lipoyang/M5Gurdy/src/Icon_Volume.h

const unsigned short ICON_VOLUME[] = {
    // w,h: 36 36
    0x0000,0x0000,0x0000,0x0000,0x0000,0x0000,0x0000,0x0000,
    0x0000,0x0000,0x0000,0x0000,0x0000,0x0000,0x0000,0x0000,
    0x0000,0x0000,0x0000,0x18E3,0x39C7,0x0000,0x0000,0x0000,
    0x0000,0x0000,0xA534,0xBDF7,0x2104,0x0000,0x0000,0x0000,
    0x0000,0x0000,0x0000,0x0000,
    0x0000,0x0000,0x0000,0x0000,0x0000,0x0000,0x0000,0x0000,
    0x0000,0x0000,0x0000,0x0000,0x0000,0x0000,0x0000,0x0000,
    0x0000,0x0000,0x52AA,0xF7BE,0xFFFF,0xBDD7,0x0000,0x0000,
    0x0000,0x0861,0xFFFF,0xFFFF,0xEF7D,0x39E7,0x0000,0x0000,
    0x0000,0x0000,0x0000,0x0000,
    0x0000,0x0000,0x0000,0x0000,0x0000,0x0000,0x0000,0x0000,
    0x0000,0x0000,0x0000,0x0000,0x0000,0x0000,0x0000,0x0000,
    0x0000,0x632C,0xFFFF,0xFFFF,0xFFFF,0xFFFF,0x5269,0x0000,
    0x0000,0x0000,0xB596,0xFFFF,0xFFFF,0xF7BE,0x4208,0x0000,
    0x0000,0x0000,0x0000,0x0000,
    0x0000,0x0000,0x0000,0x0000,0x0000,0x0000,0x0000,0x0000,
    0x0000,0x0000,0x0000,0x0000,0x0000,0x0000,0x0000,0x0000,
    0x7BCF,0xFFFF,0xFFFF,0xFFFF,0xFFFF,0xFFFF,0x7BEF,0x0000,
    0x0000,0x0000,0x0000,0x8410,0xFFFF,0xFFFF,0xF79E,0x2945,
    0x0000,0x0000,0x0000,0x0000,
    0x0000,0x0000,0x0000,0x0000,0x0000,0x0000,0x0000,0x0000,
    0x0000,0x0000,0x0000,0x0000,0x0000,0x0000,0x0000,0x8C71,
    0xFFFF,0xFFFF,0xFFFF,0xFFFF,0xFFFF,0xFFFF,0x8410,0x0000,
    0x0000,0x0000,0x0000,0x0000,0x632C,0xFFFF,0xFFFF,0xD6BA,
    0x0841,0x0000,0x0000,0x0000,
    0x0000,0x0000,0x0000,0x0000,0x0000,0x0000,0x0000,0x0000,
    0x0000,0x0000,0x0000,0x0000,0x0000,0x0020,0xA513,0xFFFF,
    0xFFFF,0xFFFF,0xFFFF,0xFFFF,0xFFFF,0xFFFF,0x8410,0x0000,
    0x0000,0x0000,0x0000,0x0000,0x0000,0x7BCF,0xFFFF,0xFFFF,
    0x8C71,0x0000,0x0000,0x0000,
    0x0000,0x0000,0x0000,0x0000,0x0000,0x0000,0x0000,0x0000,
    0x0000,0x0000,0x0000,0x0000,0x0841,0xAD75,0xFFFF,0xFFFF,
    0xFFFF,0xFFFF,0xFFFF,0xFFFF,0xFFFF,0xFFFF,0x8410,0x0000,
    0x0000,0x0000,0x0000,0x0000,0x0000,0x0000,0xB5B6,0xFFFF,
    0xFFDF,0x2945,0x0000,0x0000,
    0x0000,0x0000,0x0000,0x0000,0x0000,0x0000,0x0000,0x0000,
    0x0000,0x0000,0x0000,0x0861,0xBDF7,0xFFFF,0xFFFF,0xFFFF,
    0xFFFF,0xFFFF,0xFFFF,0xFFFF,0xFFFF,0xFFFF,0x8410,0x0000,
    0x0000,0x0000,0x0000,0x0000,0x0000,0x0000,0x18E3,0xF79E,
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
};
