lipoyang/M5Gurdy/src/DisplayUI.cpp

#include <M5Stack.h>
#include <PollingTimer.h>
#include "DisplayUI.h"
#include "Icon_Scale.h"
#include "Icon_Volume.h"

// 外部参照
extern int master_vol;      // マスター音量
extern int tone_no;         // 音色
extern int scale;           // 音階(ハ長調からどれだけ上がるか下がるか)

// 描画位置
#define X_TONE      10
#define Y_TONE      10
#define W_TONE      300
#define P_TONE      24
#define X_SCALE     10
#define Y_SCALE     170
#define W_SCALE     140
#define P_SCALE     60
#define X_VOLUME    170
#define Y_VOLUME    170
#define W_VOLUME    140
#define P_VOLUME    60
#define X_KEY       120
#define Y_KEY       80
#define W_KEY       100
#define H_KEY       64
#define H_CHAR      48
#define R_CHAR      5
#define X_ERROR     10
#define Y_ERROR1    65
#define Y_ERROR2    115
#define W_ERROR     300
#define H_ERROR     100
#define P_ICON      12

// スプライト
TFT_eSprite spriteKey    = TFT_eSprite(&M5.Lcd);
TFT_eSprite spriteTone   = TFT_eSprite(&M5.Lcd);
TFT_eSprite spriteScale  = TFT_eSprite(&M5.Lcd);
TFT_eSprite spriteVolume = TFT_eSprite(&M5.Lcd);
TFT_eSprite spriteError  = TFT_eSprite(&M5.Lcd);

// ポップアップ表示
bool isPopup = false;
OneShotTimer popupTimer;

// サブルーチン
static void DisplayUI_frame();
static void DisplayUI_sound(int octave, int key12, int vol);

// 初期化
void DisplayUI_begin()
{
    M5.begin(true, false, true); // LCD:ON, SDカード:OFF, シリアル:ON
//  M5.Power.begin();
//  M5.Speaker.setVolume(0);
//  M5.Lcd.setBrightness(200);
    M5.Lcd.setRotation(3); // 180度回転

    M5.Lcd.fillScreen(BLACK);

    // スプライトの作成
    spriteKey.setColorDepth(16);
    spriteKey.createSprite(W_KEY, H_KEY);
    spriteKey.setTextFont(2);
    spriteKey.setTextSize(4);

    spriteTone.setColorDepth(16);
    spriteTone.createSprite(W_TONE - P_TONE, H_CHAR);
    spriteTone.setTextFont(2);
    spriteTone.setTextSize(3);

    spriteScale.setColorDepth(16);
    spriteScale.createSprite(W_SCALE - P_SCALE, H_CHAR);
    spriteScale.setTextFont(2);
    spriteScale.setTextSize(3);

    spriteVolume.setColorDepth(16);
    spriteVolume.createSprite(W_VOLUME - P_VOLUME, H_CHAR);
    spriteVolume.setTextFont(2);
    spriteVolume.setTextSize(3);

    spriteError.setColorDepth(16);
    spriteError.createSprite(W_ERROR, H_ERROR);
    spriteError.setTextFont(2);
    spriteError.setTextSize(3);

    DisplayUI_frame();
    DisplayUI_settings();
}

// メインループ処理
void DisplayUI_loop(int octave, int key12, int vol)
{
    M5.update();
    
    // ボタン入力判定とそれに対する処理
    if (M5.BtnA.wasPressed()) {
    }
    if (M5.BtnB.wasPressed()){
    }
    if(M5.BtnC.wasPressed()){
    }
    
    // サウンド出力の描画
    static int cnt = 0;
    cnt++;
    if(cnt >= 4){
        cnt = 0;
        if(!isPopup){
            DisplayUI_sound(octave, key12, vol);
        }
    }
    // ポップアップの解除
    if(isPopup && popupTimer.elapsed()){
        isPopup = false;
        DisplayUI_error("");
    }
}

// 枠線の描画
static void DisplayUI_frame()
{
    M5.Lcd.drawRoundRect(
        X_TONE - R_CHAR, Y_TONE - R_CHAR,
        W_TONE + R_CHAR * 2, H_CHAR + R_CHAR * 2,
        R_CHAR, WHITE);//YELLOW); 
    M5.Lcd.drawRoundRect(
        X_SCALE - R_CHAR, Y_SCALE - R_CHAR,
        W_SCALE + R_CHAR * 2, H_CHAR + R_CHAR * 2,
        R_CHAR, WHITE);//YELLOW); 
    M5.Lcd.drawRoundRect(
        X_VOLUME - R_CHAR, Y_VOLUME - R_CHAR,
        W_VOLUME + R_CHAR * 2, H_CHAR + R_CHAR * 2,
        R_CHAR, WHITE);//YELLOW); 

    M5.Lcd.drawBitmap(X_TONE + P_ICON, Y_SCALE + 6, 36, 36, ICON_SCALE);
    M5.Lcd.drawBitmap(X_VOLUME + P_ICON, Y_SCALE + 6, 36, 36, ICON_VOLUME);
}

// 設定の描画
void DisplayUI_settings()
{
    // 音色名
    static const char TONE_NAME[][13] = {
        "Strings",
        "Bagpipes",
        "Church Organ",
        "Accordion",
        "Flute",
        "Trumpet",
        "Synthesizer",
        "String Synth",
        "Chorus",
    };

    // 音色
    spriteTone.setTextColor(YELLOW); //, BLACK);
    spriteTone.fillRect(0,0,W_TONE - P_TONE,H_CHAR,BLACK);
    spriteTone.setCursor(0,0);
    spriteTone.print(TONE_NAME[tone_no]);
    spriteTone.pushSprite(X_TONE + P_TONE, Y_TONE);

    // 調性
    spriteScale.setTextColor(YELLOW); //, BLACK);
    spriteScale.fillRect(0,0,W_SCALE - P_SCALE,H_CHAR,BLACK);
    spriteScale.setCursor(0,0);
    if(scale > 0){
        spriteScale.printf("+%d", scale);
    }else{
        spriteScale.printf("%d", scale);
    }
    spriteScale.pushSprite(X_SCALE + P_SCALE, Y_SCALE);

    // 音量
    spriteVolume.setTextColor(YELLOW); //, BLACK);
    spriteVolume.fillRect(0,0,W_VOLUME - P_VOLUME,H_CHAR,BLACK);
    spriteVolume.setCursor(0,0);
    // int vol = (master_vol >= 32) ? master_vol - 31 : 0;
    spriteVolume.printf("%d", master_vol);
    spriteVolume.pushSprite(X_VOLUME + P_VOLUME, Y_VOLUME);
}

// サウンドの描画
static void DisplayUI_sound(int octave, int key12, int vol)
{
    // オクターブごとの表示色のRGB値 (M5の色定数は5:6:5の16ビットカラー)
    static const uint16_t COLOR_TABLE[][3] = {
        { (RED    >> 11) & 0x1F, (RED    >> 5) & 0x3F, RED    & 0x1F }, // O2 赤色
        { (ORANGE >> 11) & 0x1F, (ORANGE >> 5) & 0x3F, ORANGE & 0x1F }, // O3 オレンジ色
        { (YELLOW >> 11) & 0x1F, (YELLOW >> 5) & 0x3F, YELLOW & 0x1F }, // O4 黄色
        { (GREEN  >> 11) & 0x1F, (GREEN  >> 5) & 0x3F, GREEN  & 0x1F }, // O5 緑色
        { (CYAN   >> 11) & 0x1F, (CYAN   >> 5) & 0x3F, CYAN   & 0x1F }, // O6 水色
    };
    // 音階の名前
    static const char KEY_NAME[12][3] = {
      "C", "C#", "D", "D#", "E", "F", "F#", "G", "G#", "A", "A#", "B" 
    };
    
    // 音量によって明度を変える
    int index = octave - 2;
    uint16_t r = COLOR_TABLE[index][0];
    uint16_t g = COLOR_TABLE[index][1];
    uint16_t b = COLOR_TABLE[index][2];
    const int VOL_SAT = 64; // 127以下の値で調整
    if(vol > VOL_SAT) vol = VOL_SAT;
    r = r * vol / VOL_SAT;
    g = g * vol / VOL_SAT;
    b = b * vol / VOL_SAT;
    uint16_t color = (r << 11) | (g << 5) | b;
    
#if 0
    M5.Lcd.fillRect(X_KEY,Y_KEY,W_KEY,H_KEY,BLACK);
    M5.Lcd.setTextColor(color);//, BLACK);
    M5.Lcd.setCursor(X_KEY,Y_KEY);
    M5.Lcd.setTextFont(2);
    M5.Lcd.setTextSize(4);
    M5.Lcd.print(KEY_NAME[key12]);
#else
    spriteKey.fillRect(0,0,W_KEY,H_KEY,BLACK);
    spriteKey.setTextColor(color);//, BLACK);
    spriteKey.setCursor(0,0);
    spriteKey.print(KEY_NAME[key12]);
    spriteKey.pushSprite(X_KEY, Y_KEY); 
#endif
}

// エラー表示
void DisplayUI_error(const char* error)
{
    spriteError.setTextColor(RED);
    
    spriteError.fillRect(0,0,W_ERROR,H_ERROR,BLACK);
    
    if(error[0] != 0x00){
        spriteError.setCursor(0,0);
        spriteError.print("ERROR");
        spriteError.setCursor(0,Y_ERROR2 - Y_ERROR1);
        spriteError.print(error);
    }
    spriteError.pushSprite(X_ERROR, Y_ERROR1); 
}

// ドローンモード表示
void DisplayUI_droneMode(int mode)
{
    static const char* CHANTER_INFO[] = {
        " 2 Chanters",
        " 2 Chanters",
        " 2 Chanters",
        " H Chanter",
        " H Chanter",
        " L Chanter",
        " L Chanter",
    };
    static const char* DRONE_INFO[] = {
        " 4 Drones",
        " 2 Drones",
        " No Drone",
        " 2 Drones",
        " No Drone",
        " 2 Drones",
        " No Drone",
    };

    spriteError.setTextColor(GREEN);
    spriteError.fillRect(0,0,W_ERROR,H_ERROR,BLACK);
    
    spriteError.setCursor(0,0);
    spriteError.print(CHANTER_INFO[mode]);
    spriteError.setCursor(0,Y_ERROR2 - Y_ERROR1);
    spriteError.print(DRONE_INFO[mode]);

    spriteError.pushSprite(X_ERROR, Y_ERROR1);

    isPopup = true;
    popupTimer.set(1000);
}
